sparkfunX/ARGOS-ARTIC-R2-Shield/img/17236-Artic_R2_Breakout-04.jpg

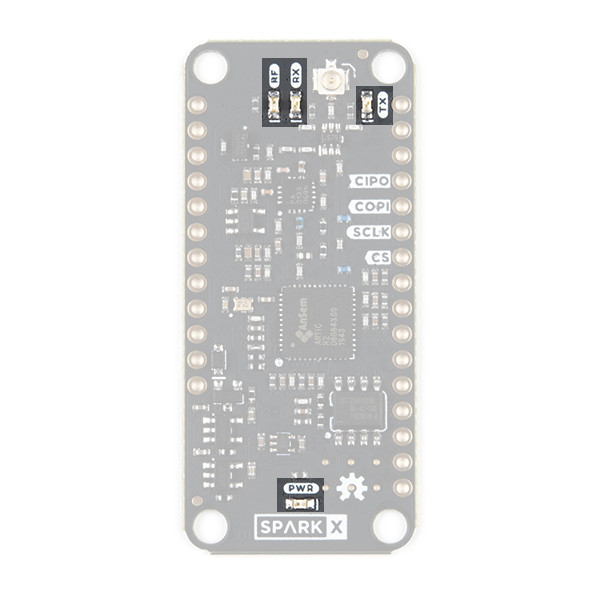
img/17236-Artic_R2_Breakout-04.jpg
