sparkfunX/ARGOS-ARTIC-R2-Shield/img/Bottom.JPG

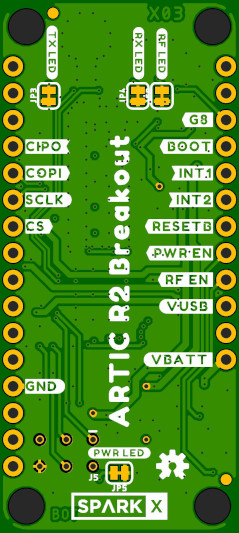
img/Bottom.JPG
