sparkfunX/ARGOS-ARTIC-R2-Shield/img/HookUp1.JPG

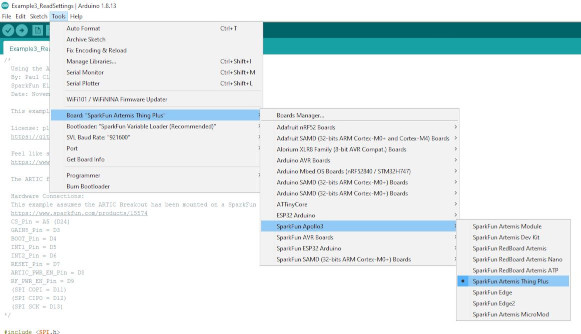
img/HookUp1.JPG
