sparkfunX/ARGOS-ARTIC-R2-Shield/img/HookUp2.JPG

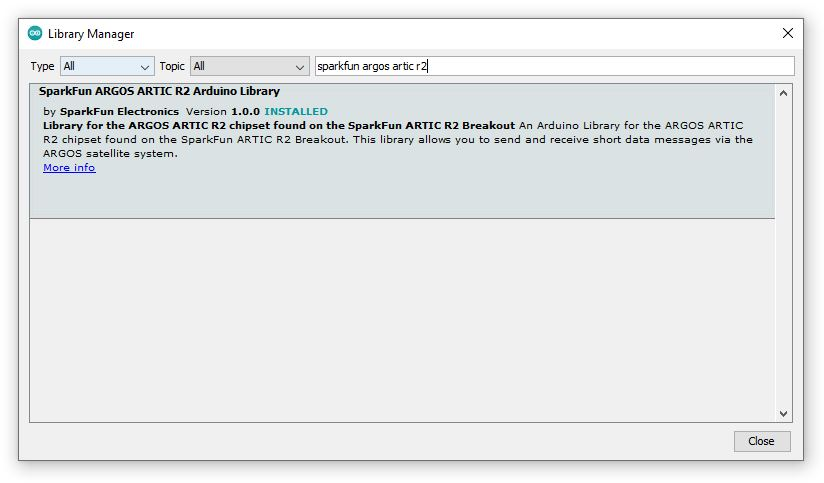
img/HookUp2.JPG
