sparkfunX/ARGOS-ARTIC-R2-Shield/img/HookUp4.JPG

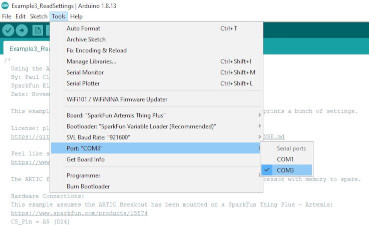
img/HookUp4.JPG
